bgilsrud/arduino_focuser_tmc2130/Brackets/Sky-Watcher Newton Crayford/1.jpg

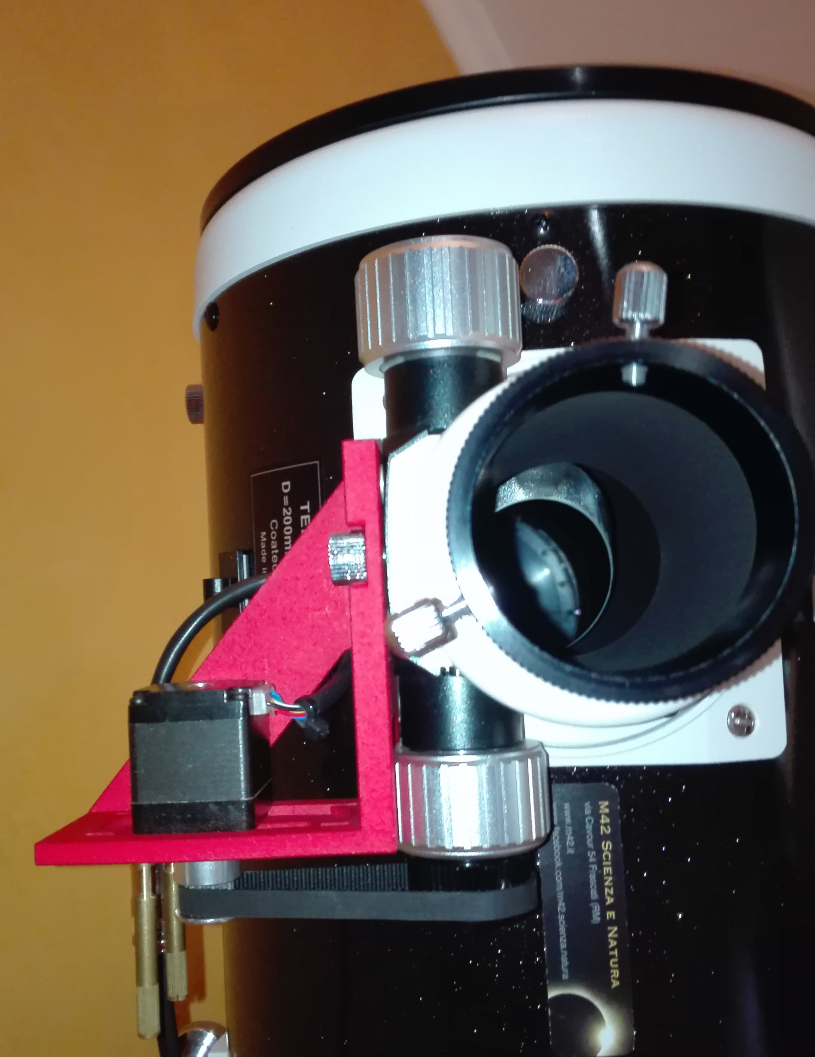
Brackets/Sky-Watcher Newton Crayford/1.jpg
