bgilsrud/arduino_focuser_tmc2130/Brackets/Sky-Watcher Newton Crayford/2.jpg

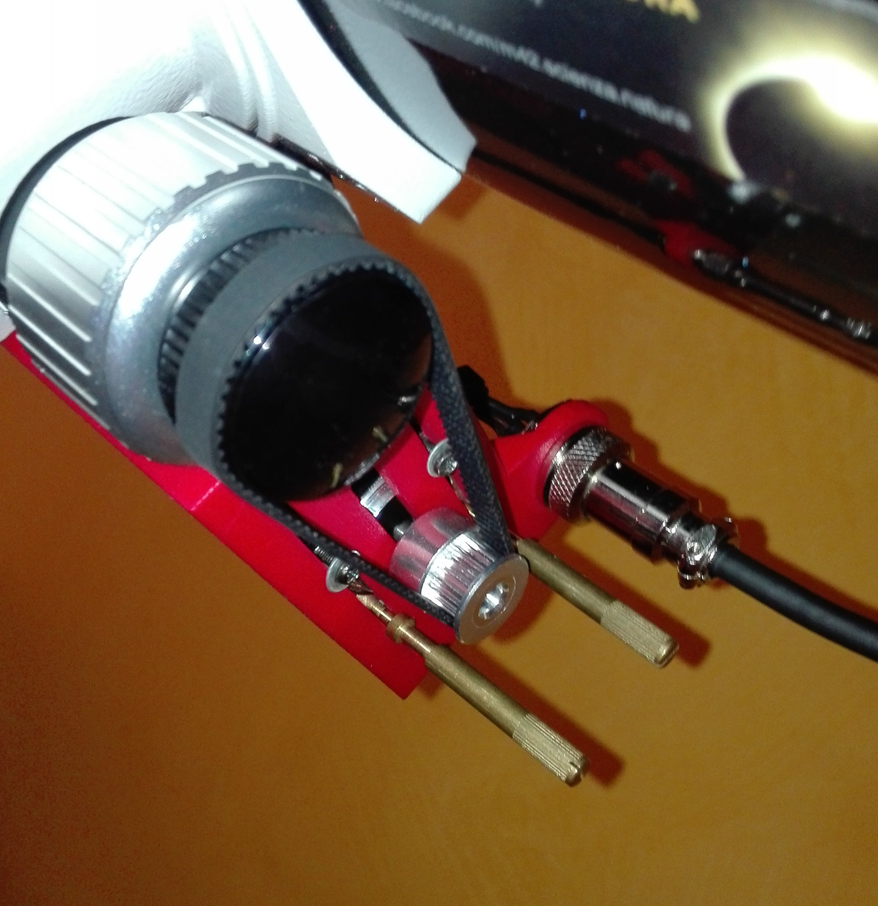
Brackets/Sky-Watcher Newton Crayford/2.jpg
