bgilsrud/arduino_focuser_tmc2130/Docs/2.jpg

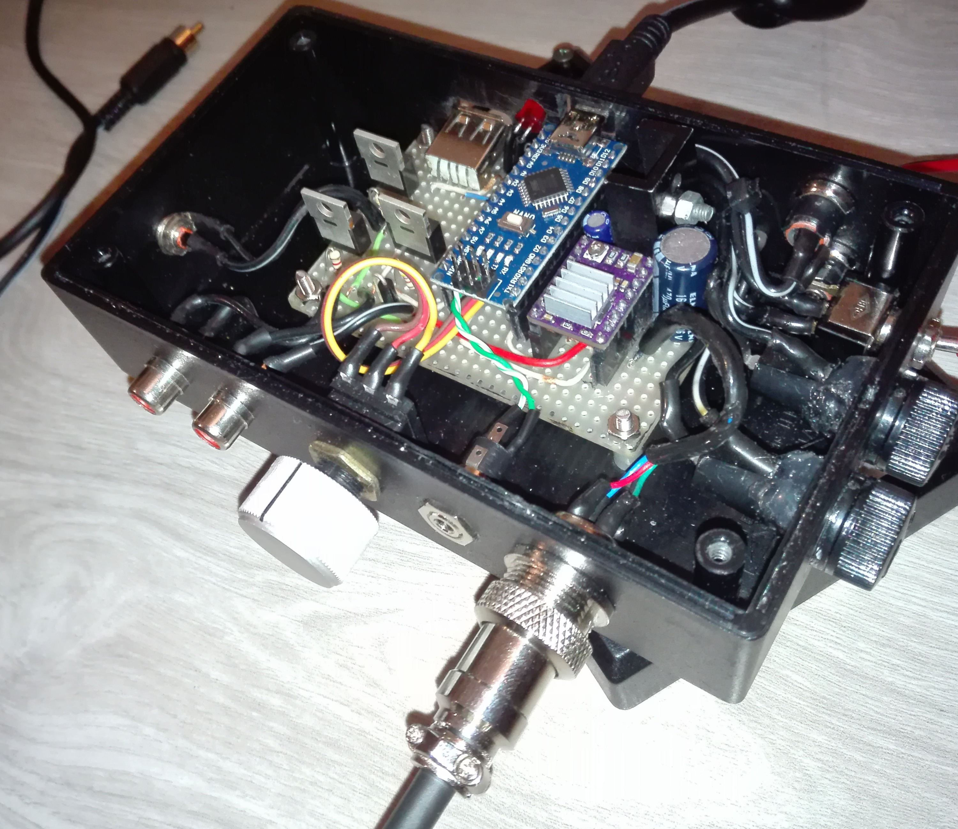
Docs/2.jpg
